CTI-ru1/iot-nodes/UberdustSensors/UberdustSensors.h

#include <Sensor.h>
#include "LightSensor.h"
#include "CurrentSensor2.h"
#include "LM35Sensor.h"
#include "HumiditySensorLM35.h"
#include "PirSensor.h"
#include "LightDigital.h"
#include "TemDigital.h"
#include "HumDigital.h"
#include "SoundGrove.h"
#include "CoSensor.h"
#include "MethaneSensor.h"
#include "SoundGroveSample.h"
