CTI-ru1/iot-nodes/UberdustSensors/resource.h

#ifndef RESOURCE_H
#define RESOURCE_H

#include <Arduino.h>
#include "Sensor.h"

class Resource {
public:

    Resource();
    /**
     * Resource Constructor. User to pass as parameters all required fields: 
     *
     */
    Resource(Sensor * sensor);
    /**
     * Called when a resouce is to be evaluated again.
     */
   
    char * name();
    /**
     * Length of the resource's name.
     */
    uint8_t name_length();
    /**
     * Check if the resource allows the method.
     */
    void get_value( char* output_data, uint8_t& output_data_len); 	
    //bool check();
    bool periodic_check();
    void check_and_send();	

private:
 
    Sensor *_sensor;
    
};
#endif
